kurs0n/HabCube/frontend/HabCube/assets/ConceptViews/1.png

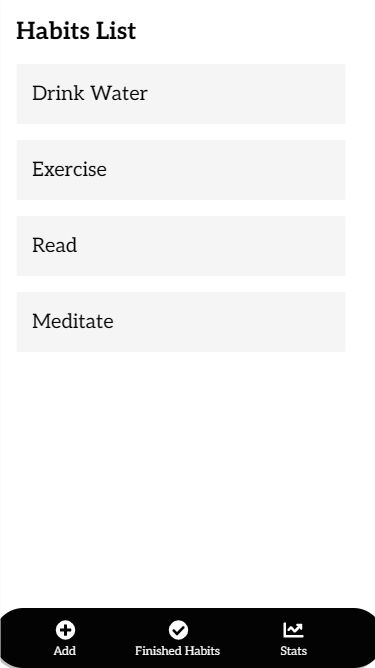
frontend/HabCube/assets/ConceptViews/1.png
