kurs0n/HabCube/frontend/HabCube/assets/ConceptViews/2.png

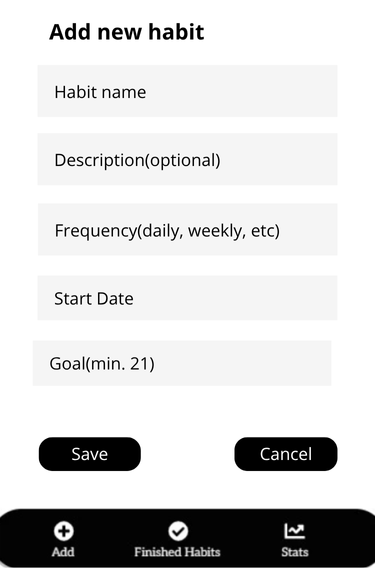
frontend/HabCube/assets/ConceptViews/2.png
