kurs0n/HabCube/frontend/HabCube/assets/ConceptViews/3.png

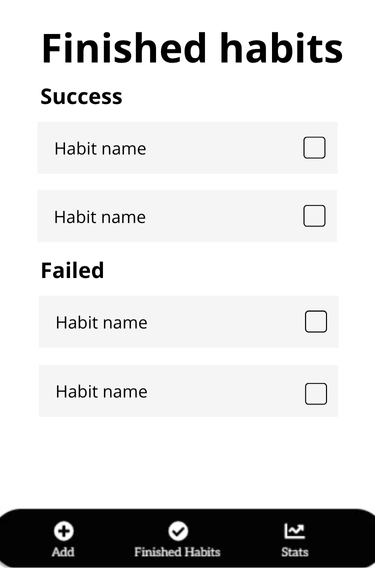
frontend/HabCube/assets/ConceptViews/3.png
