kurs0n/HabCube/frontend/HabCube/assets/ConceptViews/4.png

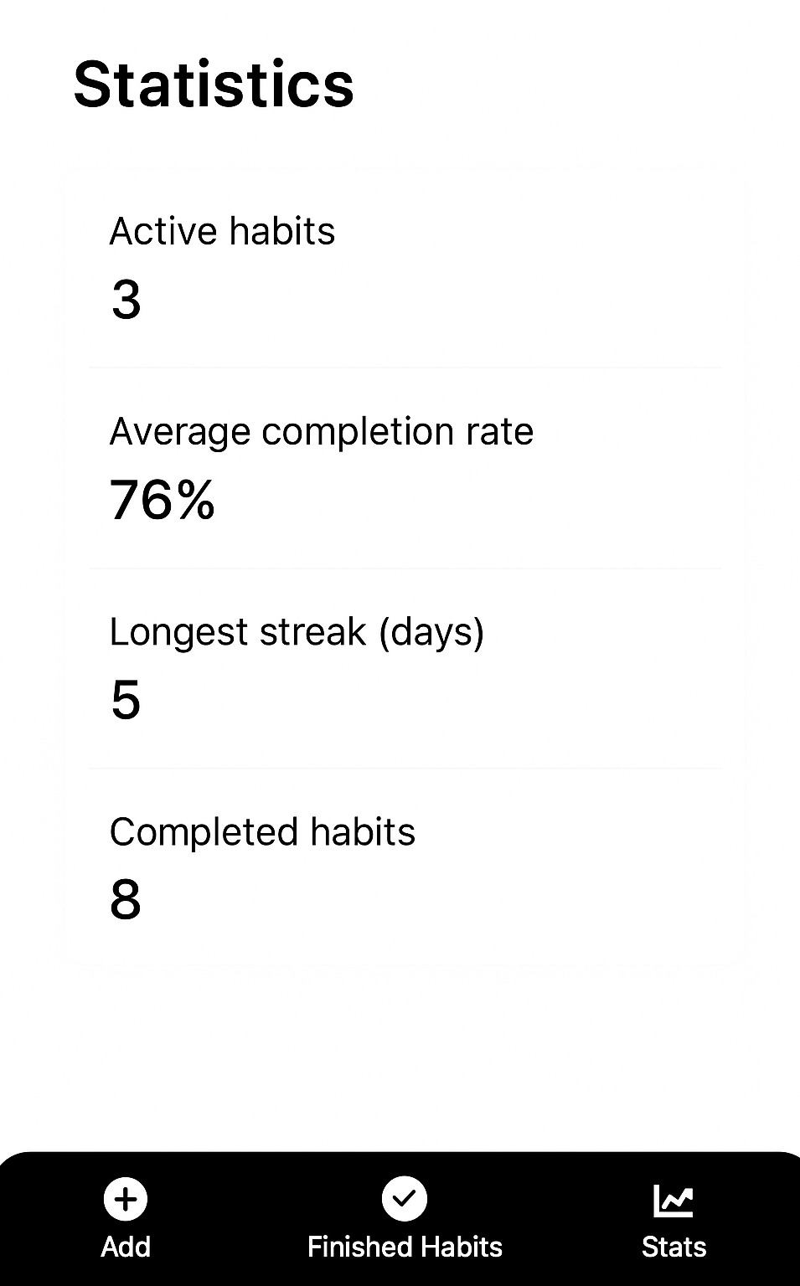
frontend/HabCube/assets/ConceptViews/4.png
